jedimatt42/mister-case/images/bottom.png

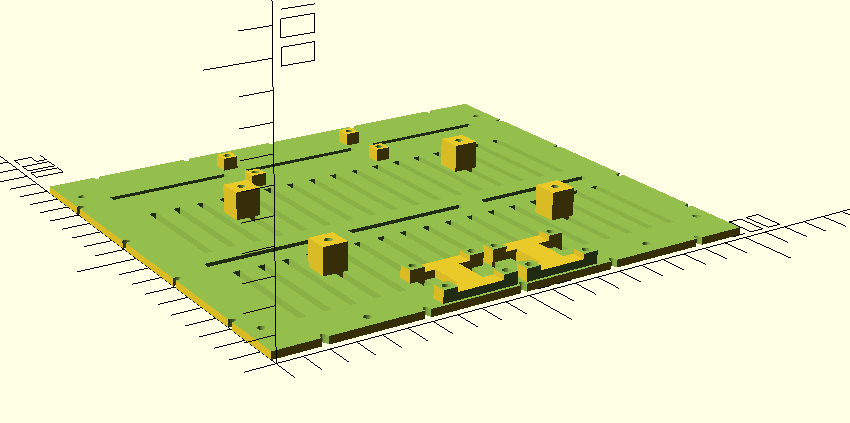
images/bottom.png
