jedimatt42/mister-case/images/button.png

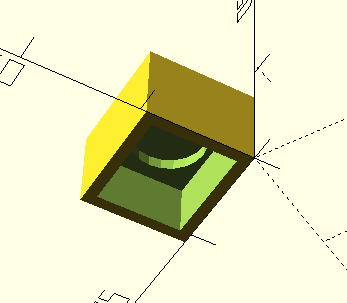
images/button.png
