jedimatt42/mister-case/images/front-center.png

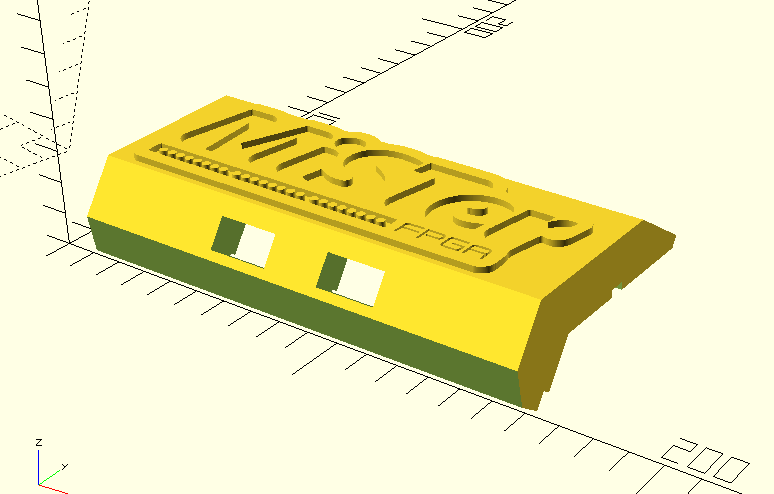
images/front-center.png
