jedimatt42/mister-case/images/left-seam.png

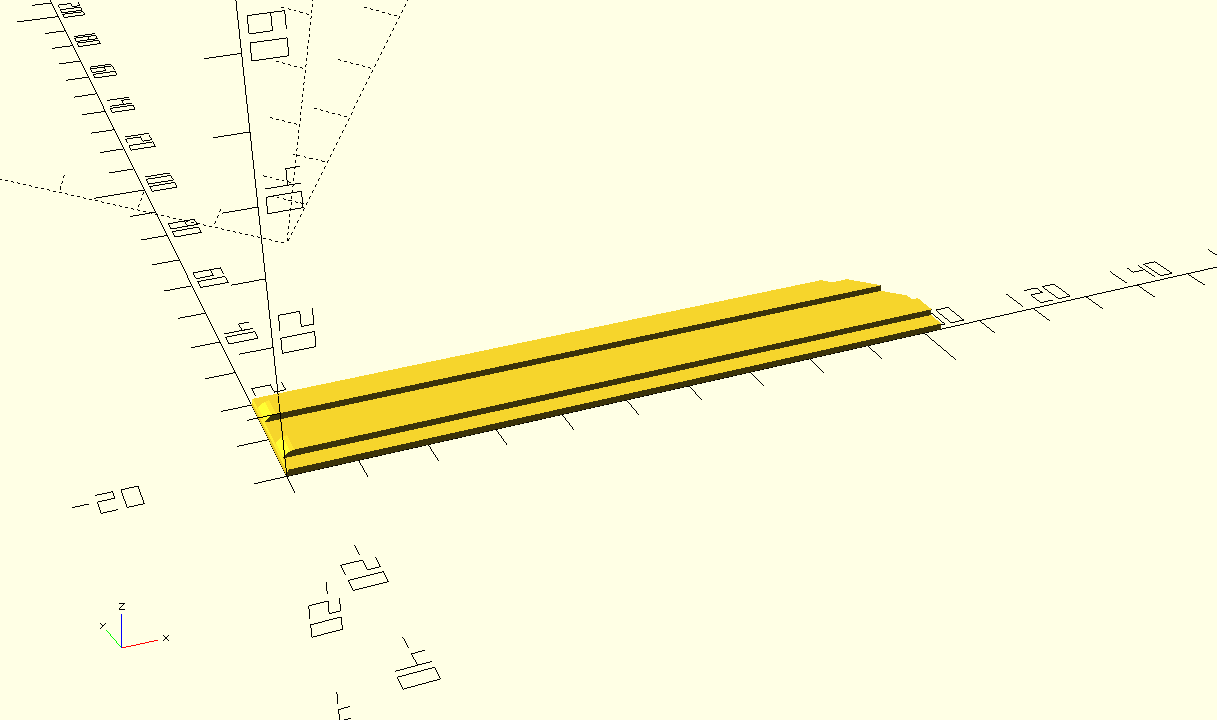
images/left-seam.png
