jedimatt42/mister-case/images/middle-seam.png

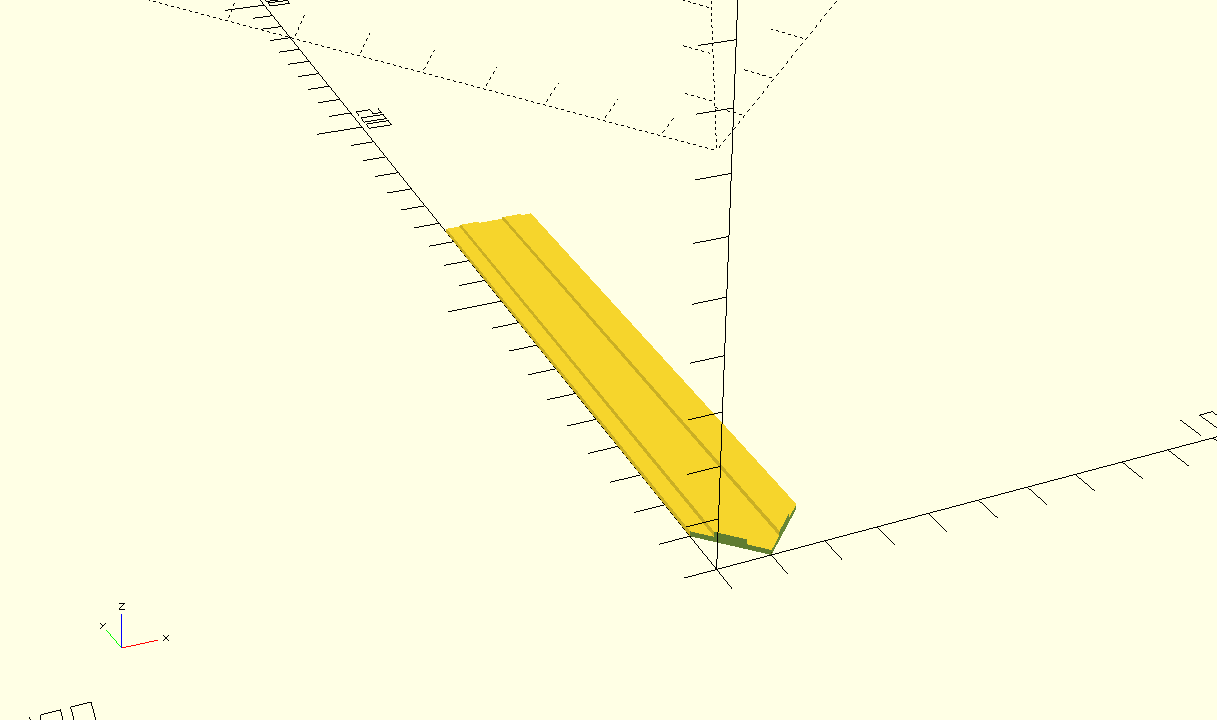
images/middle-seam.png
