jedimatt42/mister-case/images/sides.png

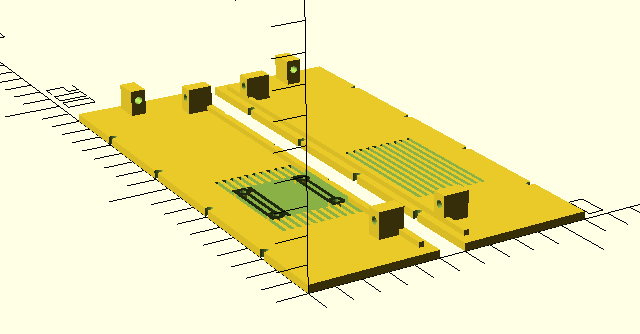
images/sides.png
