jedimatt42/mister-case/images/parts.png

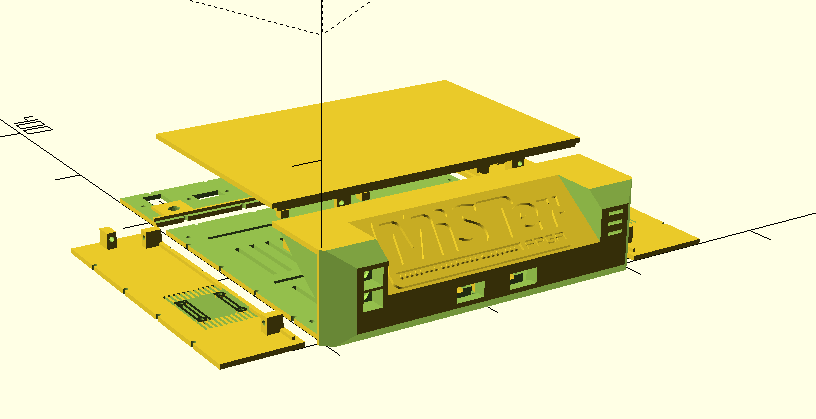
images/parts.png
